modx-arseniy/leylabella/STLs/3 - ribs.stl

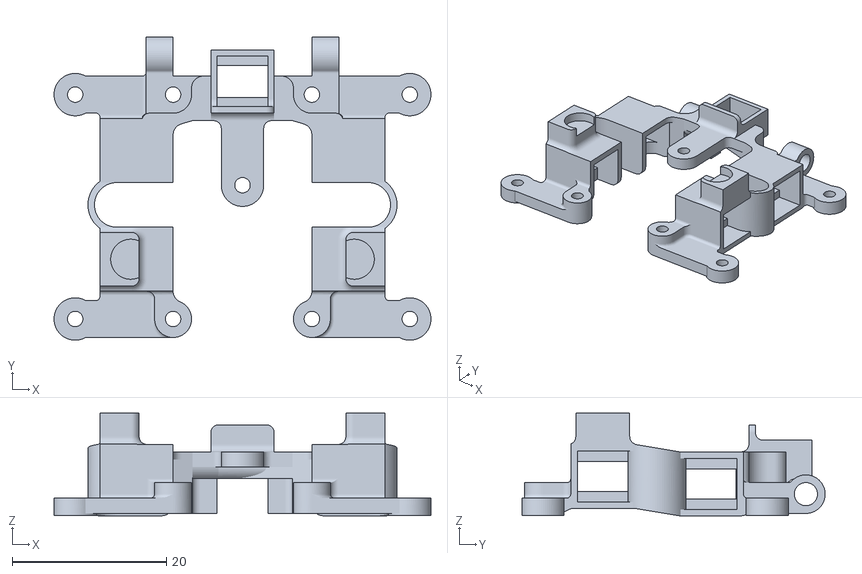
[picture p35: CAD file, 2025-08-16]
STLs/3 - ribs.stl
48.9 x 39.3 x 13.3
